greenlaver/CERS-terminal/src/CERS-terminal/SJIS2UTF8.cpp

#include "SJIS2UTF8.h"

bool convertSjis2UTF8(uint32_t max_len, char *str_sjis, char *str_utf8)
{
    for (int i = 0; i < max_len; i++)
    {
        switch (str_sjis[i])
        {
        case 0x00:
            *str_utf8 = 0x00;
            return true;
        case 0x20:
            *str_utf8++ = ' ';
            break;
        case 0xA6: // ヲ
            *str_utf8++ = 0xE3;
            *str_utf8++ = 0x83;
            *str_utf8++ = 0xB2;
            break;
        case 0xA7: // ァ
            *str_utf8++ = 0xE3;
            *str_utf8++ = 0x82;
            *str_utf8++ = 0xA1;
            break;
        case 0xA8: // ィ
            *str_utf8++ = 0xE3;
            *str_utf8++ = 0x82;
            *str_utf8++ = 0xA3;
            break;
        case 0xA9: // ゥ
            *str_utf8++ = 0xE3;
            *str_utf8++ = 0x82;
            *str_utf8++ = 0xA5;
            break;
        case 0xAA: // ェ
            *str_utf8++ = 0xE3;
            *str_utf8++ = 0x82;
            *str_utf8++ = 0xA7;
            break;
        case 0xAB: // ォ
            *str_utf8++ = 0xE3;
            *str_utf8++ = 0x82;
            *str_utf8++ = 0xA9;
            break;
        case 0xAC: // ャ
            *str_utf8++ = 0xE3;
            *str_utf8++ = 0x83;
            *str_utf8++ = 0xA3;
            break;
        case 0xAD: // ュ
            *str_utf8++ = 0xE3;
            *str_utf8++ = 0x83;
            *str_utf8++ = 0xA5;
            break;
        case 0xAE: // ョ
            *str_utf8++ = 0xE3;
            *str_utf8++ = 0x83;
            *str_utf8++ = 0xA7;
            break;
        case 0xAF: // ッ
            *str_utf8++ = 0xE3;
            *str_utf8++ = 0x83;
            *str_utf8++ = 0x83;
            break;
        case 0xB0: // -
            *str_utf8++ = 0xE3;
            *str_utf8++ = 0x83;
            *str_utf8++ = 0xBC;
            break;
        case 0xB1: // ア
            *str_utf8++ = 0xE3;
            *str_utf8++ = 0x82;
            *str_utf8++ = 0xA2;
            break;
        case 0xB2: // イ
            *str_utf8++ = 0xE3;
            *str_utf8++ = 0x82;
            *str_utf8++ = 0xA4;
            break;
        case 0xB3: // ウ
            *str_utf8++ = 0xE3;
            *str_utf8++ = 0x82;
            *str_utf8++ = 0xA6;
            break;
        case 0xB4: // エ
            *str_utf8++ = 0xE3;
            *str_utf8++ = 0x82;
            *str_utf8++ = 0xA8;
            break;
        case 0xB5: // オ
            *str_utf8++ = 0xE3;
            *str_utf8++ = 0x82;
            *str_utf8++ = 0xAA;
            break;
        case 0xB6: // カ
            *str_utf8++ = 0xE3;
            *str_utf8++ = 0x82;
            *str_utf8++ = 0xAB;
            break;
        case 0xB7: // キ
            *str_utf8++ = 0xE3;
            *str_utf8++ = 0x82;
            *str_utf8++ = 0xAD;
            break;
        case 0xB8: // ク
            *str_utf8++ = 0xE3;
            *str_utf8++ = 0x82;
            *str_utf8++ = 0xAF;
            break;
        case 0xB9: // ケ
            *str_utf8++ = 0xE3;
            *str_utf8++ = 0x82;
            *str_utf8++ = 0xB1;
            break;
        case 0xBA: // コ
            *str_utf8++ = 0xE3;
            *str_utf8++ = 0x82;
            *str_utf8++ = 0xB3;
            break;
        case 0xBB: // サ
            *str_utf8++ = 0xE3;
            *str_utf8++ = 0x82;
            *str_utf8++ = 0xB5;
            break;
        case 0xBC: // シ
            *str_utf8++ = 0xE3;
            *str_utf8++ = 0x82;
            *str_utf8++ = 0xB7;
            break;
        case 0xBD: // ス
            *str_utf8++ = 0xE3;
            *str_utf8++ = 0x82;
            *str_utf8++ = 0xB9;
            break;
        case 0xBE: // セ
            *str_utf8++ = 0xE3;
            *str_utf8++ = 0x82;
            *str_utf8++ = 0xBB;
            break;
        case 0xBF: // ソ
            *str_utf8++ = 0xE3;
            *str_utf8++ = 0x82;
            *str_utf8++ = 0xBD;
            break;
        case 0xC0: // タ
            *str_utf8++ = 0xE3;
            *str_utf8++ = 0x82;
            *str_utf8++ = 0xBF;
            break;
        case 0xC1: // チ
            *str_utf8++ = 0xE3;
            *str_utf8++ = 0x83;
            *str_utf8++ = 0x81;
            break;
        case 0xC2: // ツ
            *str_utf8++ = 0xE3;
            *str_utf8++ = 0x83;
            *str_utf8++ = 0x84;
            break;
        case 0xC3: // テ
            *str_utf8++ = 0xE3;
            *str_utf8++ = 0x83;
            *str_utf8++ = 0x86;
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
            *str_utf8++ = 0x9B;
            break;
        case 0xDF: // ゜
            *str_utf8++ = 0xE3;
            *str_utf8++ = 0x82;
            *str_utf8++ = 0x9C;
            break;
        default:
            *str_utf8++ = '?';
            break;
        }
    }

    return false;
}
