greenlaver/CERS-terminal/src/CERS-terminal/DisplayManager.cpp

#include "DisplayManager.h"

void DisplayManager::DisplayInit(U8G2_SSD1306_128X32_UNIVISION_1_HW_I2C *_u8g2, GpioManager *gpioManager)
{
    u8g2 = _u8g2;
    gpioMan = gpioManager;
    msg_flag = true;

    msgBlinker.attach(1.5f, blinkMsg, &msg_flag);
    u8g2->begin();
    u8g2->enableUTF8Print();
}

void DisplayManager::DrawSplashScreen(const char *version)
{
    u8g2->setFontDirection(0);
    u8g2->setDrawColor(1);
    u8g2->firstPage();
    do
    {
        u8g2->setFont(u8g2_font_luBIS08_tf);
        u8g2->setCursor(10, 8);
        u8g2->print("Covid-19 Entrance");
        u8g2->setCursor(10, 18);
        u8g2->print("Recording System");

        u8g2->setFont(u8g2_font_profont12_mf);
        u8g2->setCursor(30, 32);
        u8g2->print("Ver,");
        u8g2->setCursor(60, 32);
        u8g2->print(version);
    } while (u8g2->nextPage());

    delay(2000);
}

void DisplayManager::DrawWifiConnection(char *SSID)
{
    u8g2->setFont(u8g2_font_profont12_mf);
    u8g2->setFontDirection(0);
    u8g2->firstPage();
    do
    {
        u8g2->setDrawColor(0);
        u8g2->setCursor(20, 10);
        u8g2->print(" Connect Wifi ");

        u8g2->setDrawColor(1);
        u8g2->setCursor(0, 26);
        u8g2->print(SSID);
    } while (u8g2->nextPage());
}

void DisplayManager::DrawWaitCard(char *dt_str)
{
    u8g2->setFont(u8g2_font_b16_t_japanese3);
    u8g2->setFontDirection(0);
    u8g2->setDrawColor(1);
    u8g2->firstPage();
    do
    {
        u8g2->setCursor(32, 15);
        if (gpioMan->isInMode())
            u8g2->print("入室受付");
        else
            u8g2->print("退室受付");

        if (msg_flag)
        {
            u8g2->setCursor(16, 31);
            u8g2->print("学生証タッチ");
        }
        else
        {
            char time_str[30];
            strcpy(time_str, dt_str + 11);
            time_str[8] = 0x00;

            u8g2->setCursor(32, 31);
            u8g2->print(time_str);
        }

    } while (u8g2->nextPage());
}

void DisplayManager::DrawCardInfo(char *id, char *name)
{
    u8g2->setDrawColor(1);
    u8g2->firstPage();
    do
    {
        u8g2->setFont(u8g2_font_unifont_t_japanese1);
        u8g2->setFontDirection(0);
        u8g2->setCursor(16, 10);
        u8g2->print(id);

        u8g2->setFont(u8g2_font_b12_t_japanese1);
        u8g2->setFontDirection(0);
        u8g2->setCursor(0, 30);
        u8g2->print(name);
    } while (u8g2->nextPage());
}

void DisplayManager::DrawSetupMode()
{
    u8g2->setFont(u8g2_font_profont12_mf);
    u8g2->setFontDirection(0);
    u8g2->firstPage();
    do
    {
        u8g2->setFontMode(0);
        u8g2->setDrawColor(0);

        u8g2->setCursor(25, 9);
        u8g2->print(" Setup Mode ");

        u8g2->setDrawColor(1);
        u8g2->setCursor(0, 20);
        u8g2->print("Connect usb, open COM");
        u8g2->setCursor(0, 32);
        u8g2->print("baud:115200 LF");
    } while (u8g2->nextPage());
}

void DisplayManager::DrawWifiError()
{
    u8g2->setFont(u8g2_font_b16_t_japanese3);
    u8g2->setFontDirection(0);
    u8g2->setDrawColor(1);
    u8g2->firstPage();
    do
    {
        u8g2->setCursor(32, 15);
        u8g2->print("エラー");
        u8g2->setCursor(16, 31);
        u8g2->print("WiFi切断");
    } while (u8g2->nextPage());
}

void DisplayManager::DrawNTPError()
{
    u8g2->setFont(u8g2_font_b16_t_japanese3);
    u8g2->setFontDirection(0);
    u8g2->setDrawColor(1);
    u8g2->firstPage();
    do
    {
        u8g2->setCursor(32, 15);
        u8g2->print("エラー");
        u8g2->setCursor(16, 31);
        u8g2->print("NTP失敗");
    } while (u8g2->nextPage());
}

void DisplayManager::DrawPOSTError(int code)
{
    char code_str[32];
    itoa(code, code_str, 10);

    u8g2->setFontDirection(0);
    u8g2->setFontMode(0);
    u8g2->firstPage();
    do
    {
        u8g2->setFont(u8g2_font_profont12_mf);
        u8g2->setDrawColor(0);
        u8g2->setCursor(38, 9);
        u8g2->print(" ERROR ");

        u8g2->setFont(u8g2_font_b16_t_japanese3);
        u8g2->setDrawColor(1);
        if(code == 400 || code == 409){
            u8g2->setCursor(0, 31);
            if(gpioMan->isInMode()) u8g2->print("退室して下さい！");
            else u8g2->print("入室して下さい！");
        }
        else {
            u8g2->setCursor(0, 31);
            u8g2->print("不明：");
            u8g2->setCursor(48, 31);
            u8g2->print(code_str);
        }
    } while (u8g2->nextPage());
}

void blinkMsg(bool *flag)
{
    *flag = !*flag;
}
